Z0R7N/Linearity/pdf/full_M545D.jpg

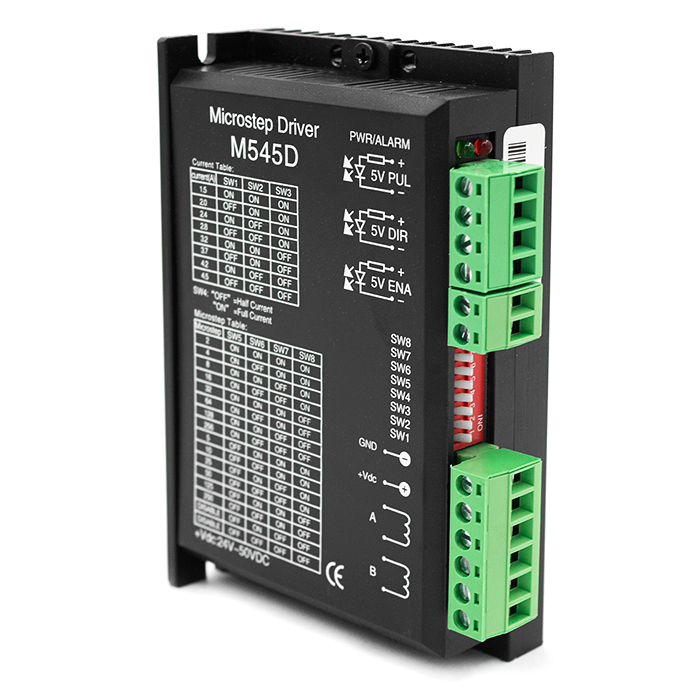
pdf/full_M545D.jpg
