Z0R7N/Linearity/3D/обработка/стойка/ncprograms/стойка д5.png

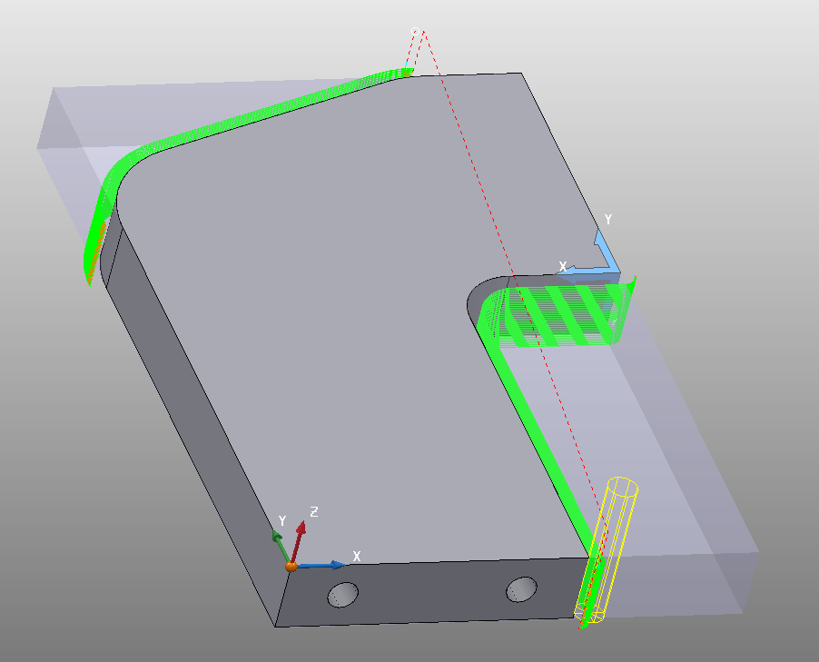
3D/обработка/стойка/ncprograms/стойка д5.png
