Z0R7N/Linearity/assets/angles.JPG

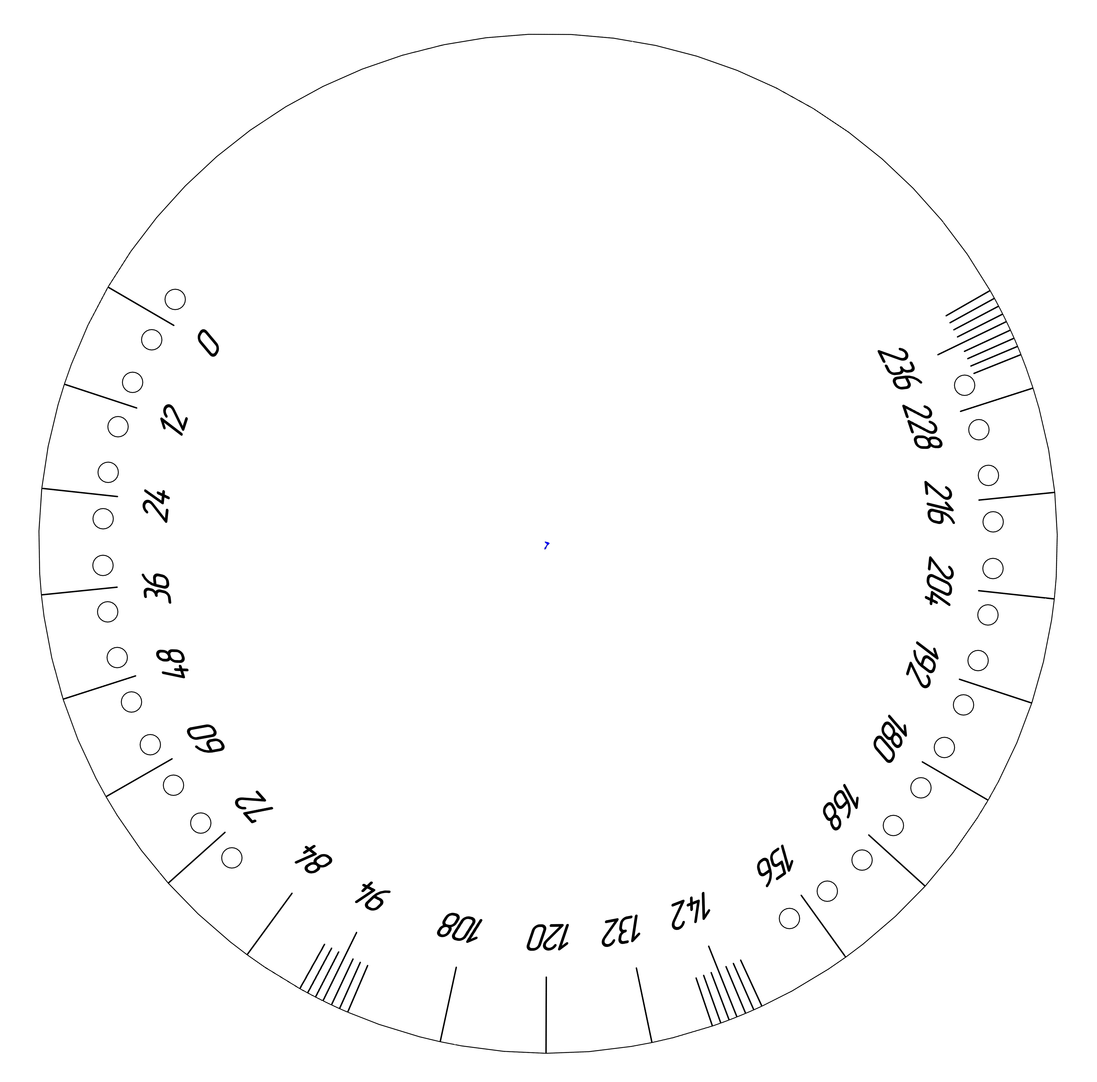
assets/angles.JPG
