Z0R7N/Linearity/assets/Nema 23.jpg

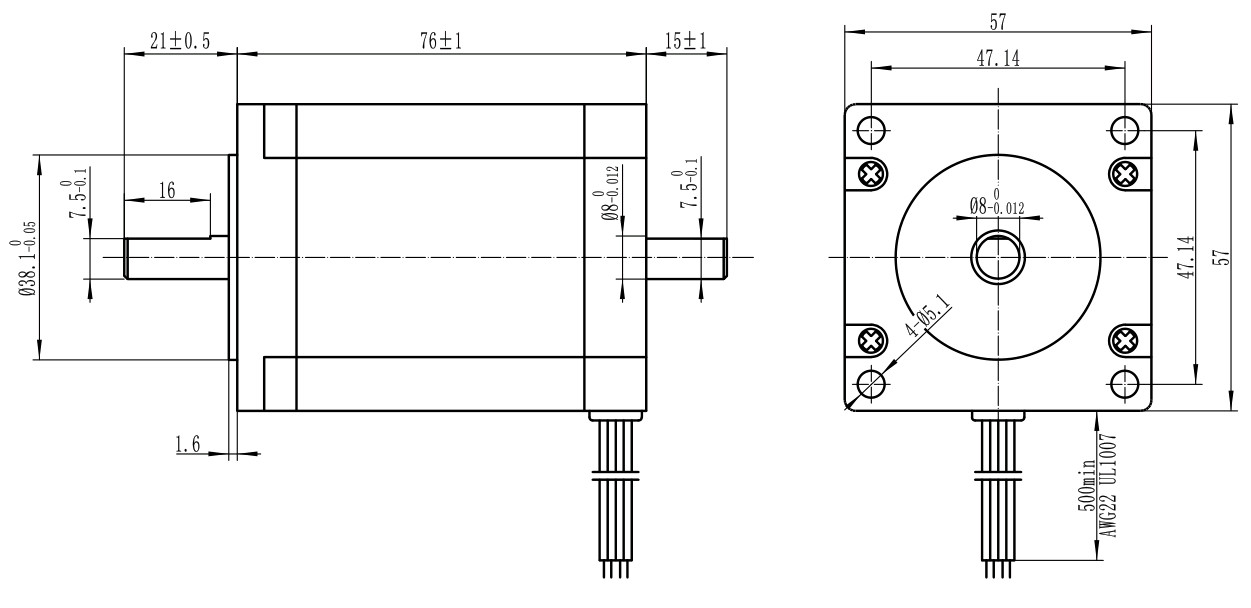
assets/Nema 23.jpg
