Z0R7N/Linearity/assets/plata pic/фреза 30гр.png

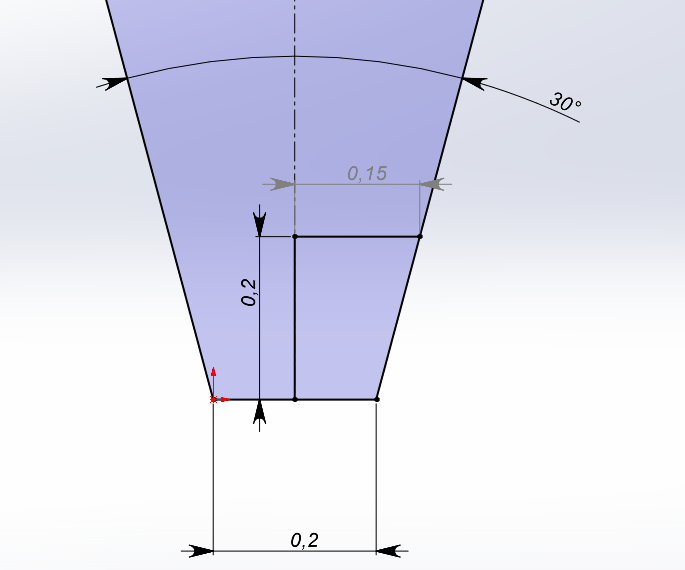
assets/plata pic/фреза 30гр.png
