Z0R7N/Linearity/assets/scheme for one angle.png

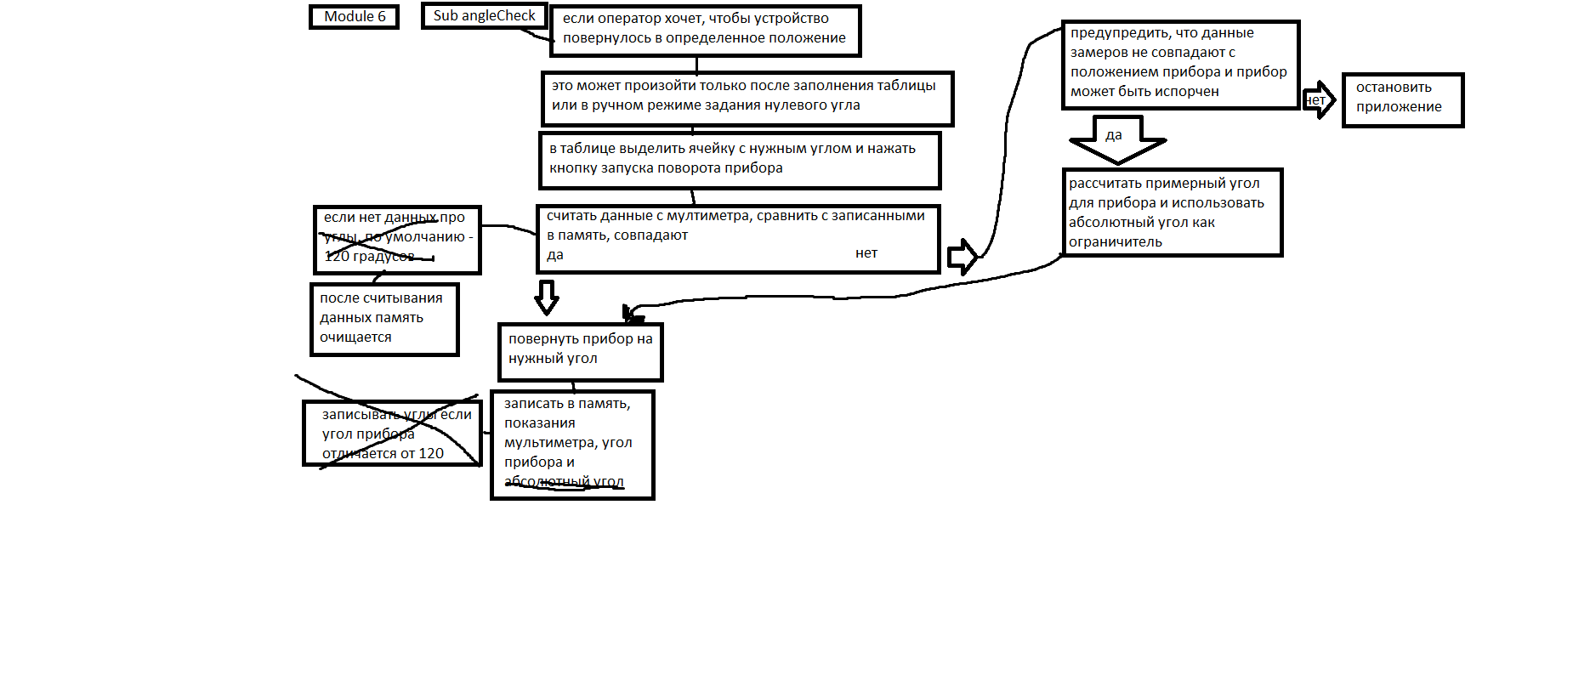
assets/scheme for one angle.png
