Z0R7N/Linearity/assets/table.png

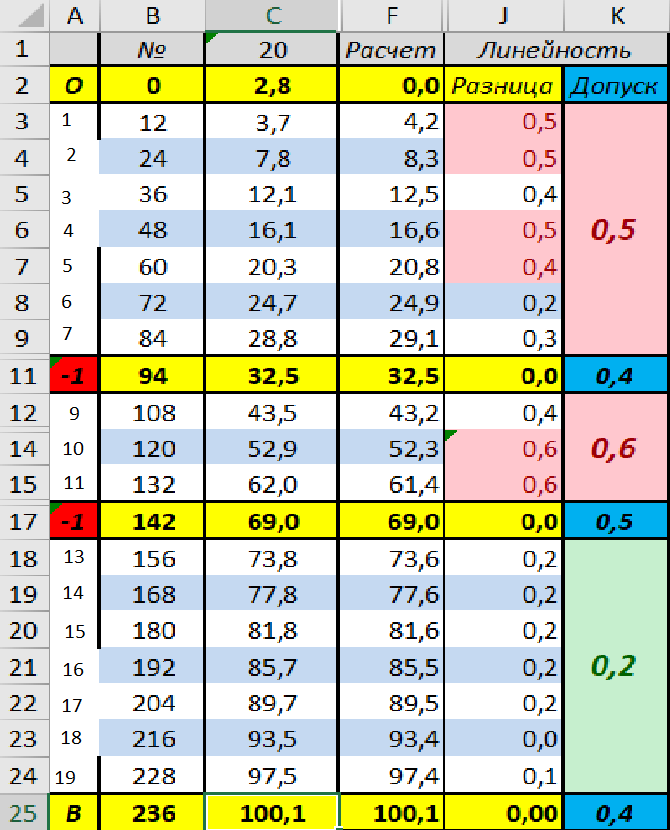
assets/table.png
