Z0R7N/Linearity/assets/usb B (2).gif

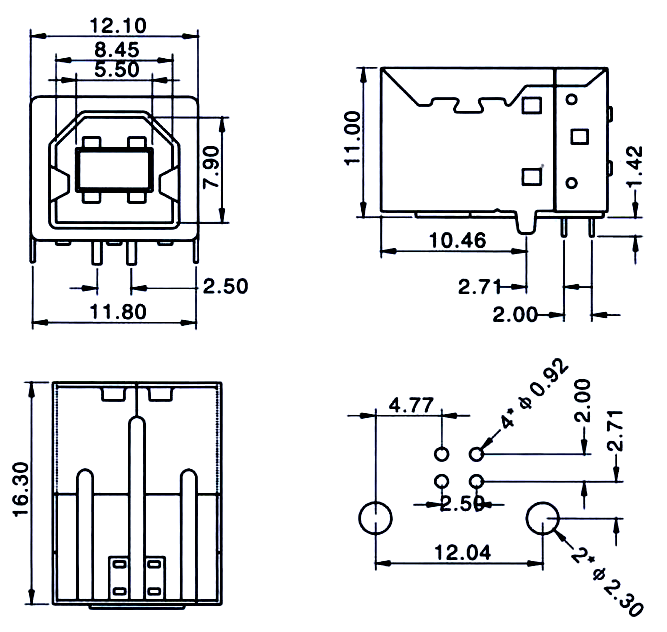
assets/usb B (2).gif
