Z0R7N/Linearity/assets/график.png

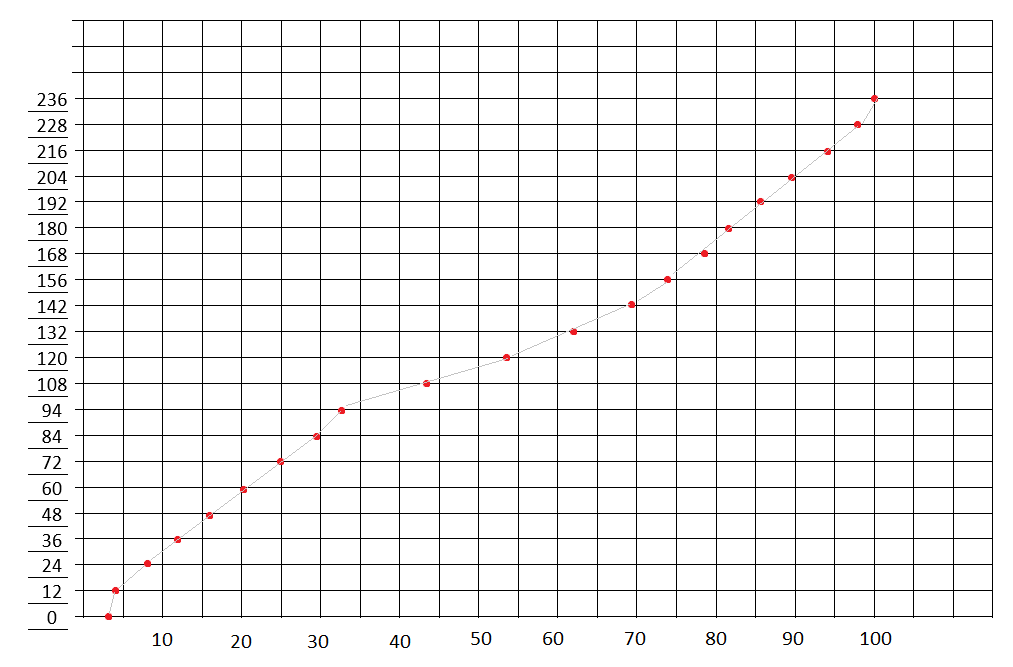
assets/график.png
