Z0R7N/Linearity/assets/прижим.jpg

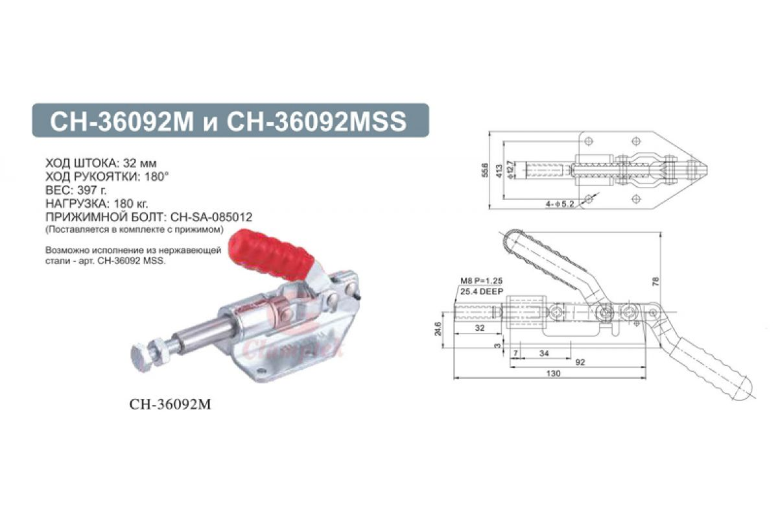
assets/прижим.jpg
