Z0R7N/Linearity/pdf/full_M545D_3.jpg

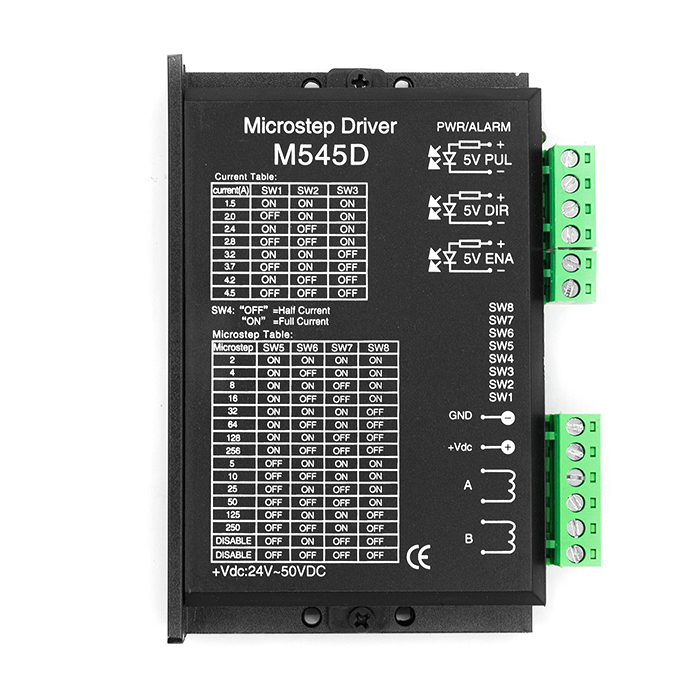
pdf/full_M545D_3.jpg
