Z0R7N/Linearity/3D/прижим.SLDPRT

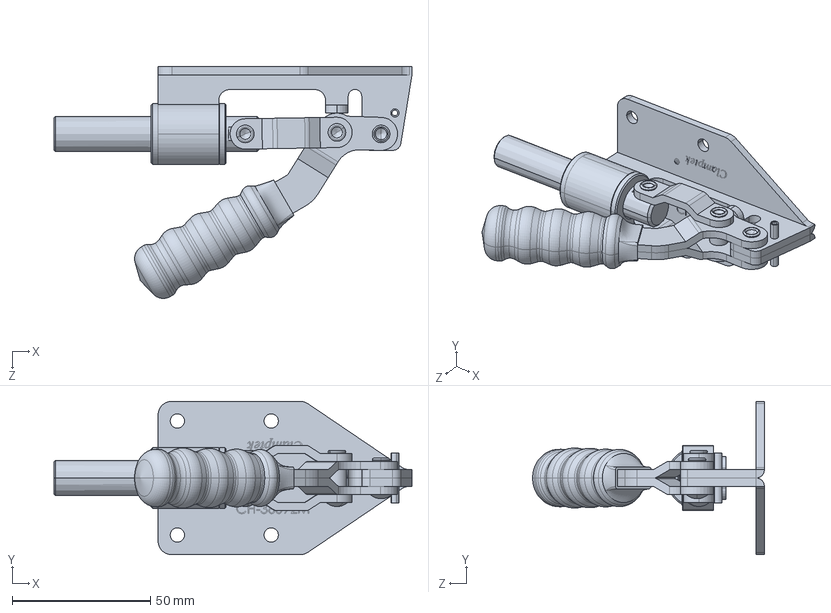
[picture p32: CAD file, 2022-04-15]
3D/прижим.SLDPRT
129.7 x 55.6 x 84.0 mm
