Z0R7N/Linearity/3D/п_крышка.stp.SLDPRT

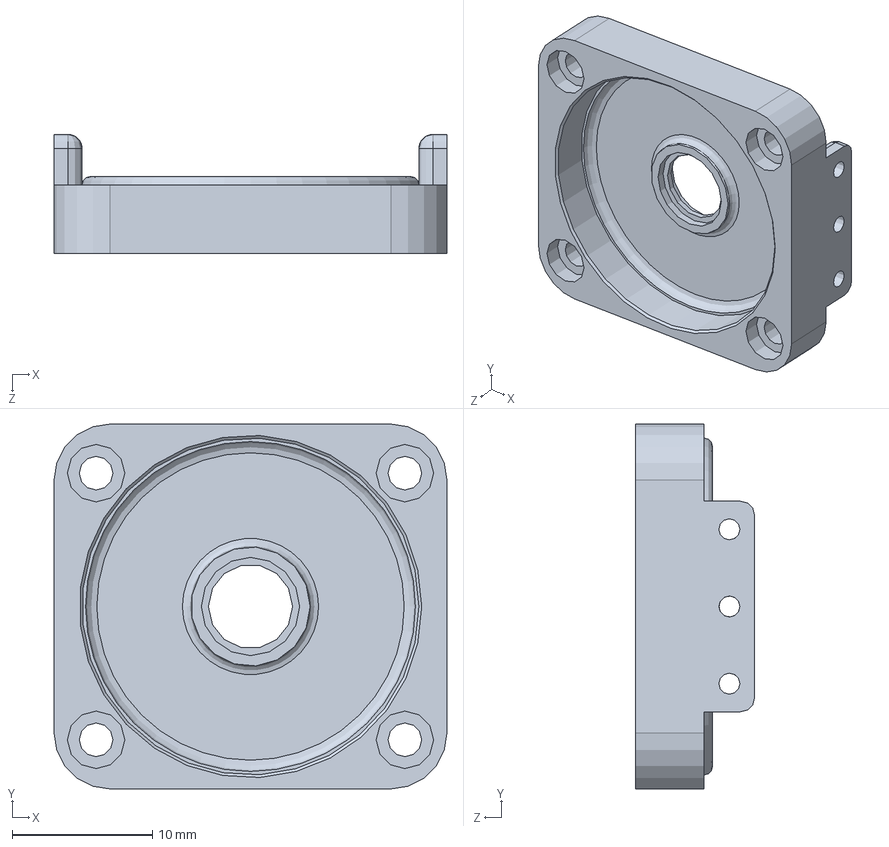
[picture p33: CAD file, 2022-04-15]
3D/п_крышка.stp.SLDPRT
28.0 x 26.0 x 8.50 mm
