Z0R7N/Linearity/3D/изолятор.SLDPRT

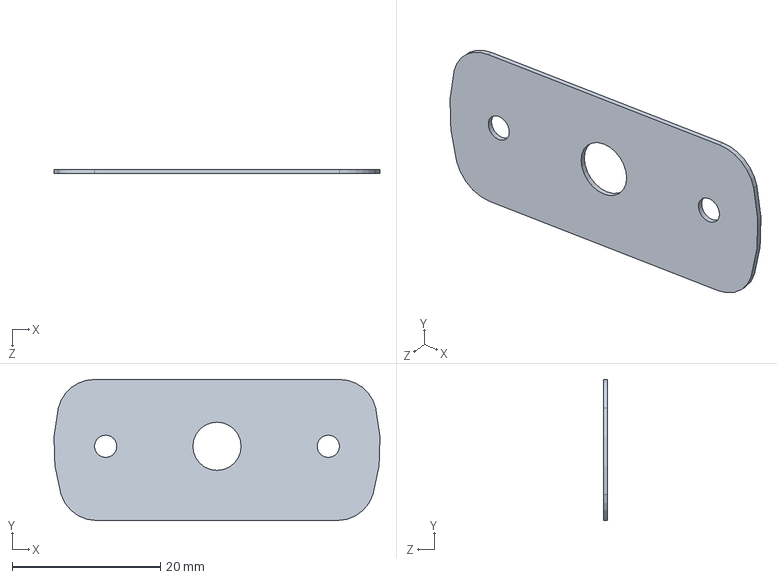
[picture p34: CAD file, 2022-04-15]
3D/изолятор.SLDPRT
43.9 x 19.0 x 0.6 mm
