Z0R7N/Linearity/3D/прижим крышки.SLDPRT

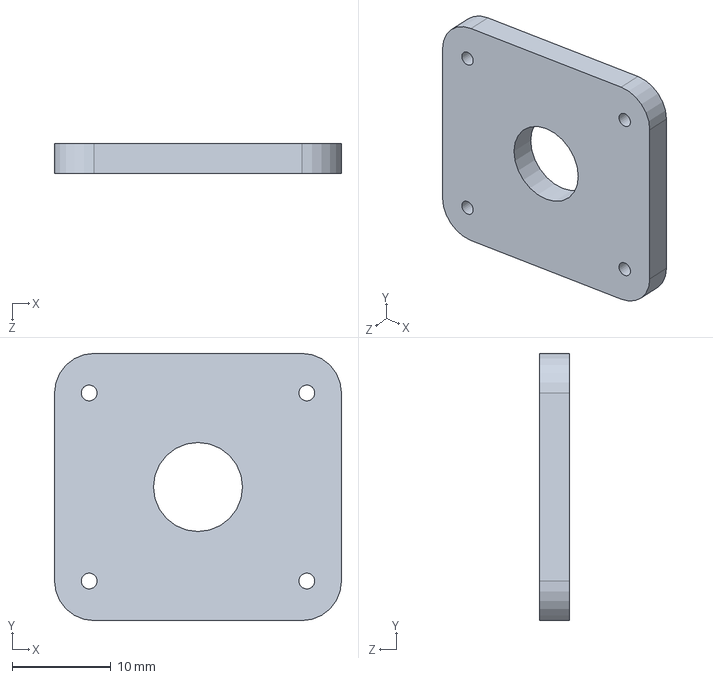
[picture p35: CAD file, 2022-04-12]
3D/прижим крышки.SLDPRT
29.0 x 27.0 x 3.00 mm
