Z0R7N/Linearity/3D/шайба прижима.SLDPRT

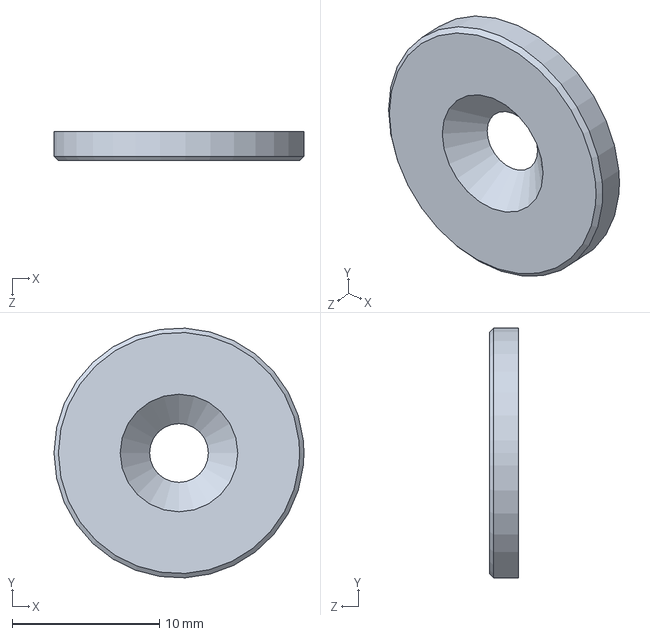
[picture p36: CAD file, 2022-04-12]
3D/шайба прижима.SLDPRT
17.0 x 17.0 x 2.00 mm
