Z0R7N/Linearity/3D/винт 2.SLDPRT

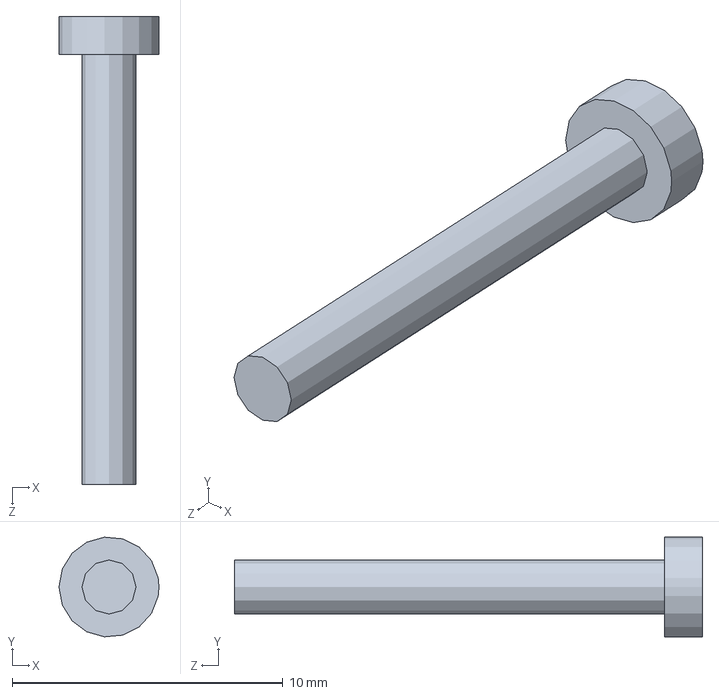
[picture p37: CAD file, 2022-04-12]
3D/винт 2.SLDPRT
3.70 x 3.68 x 17.3 mm
