Z0R7N/Linearity/3D/винт опора крышки.SLDPRT

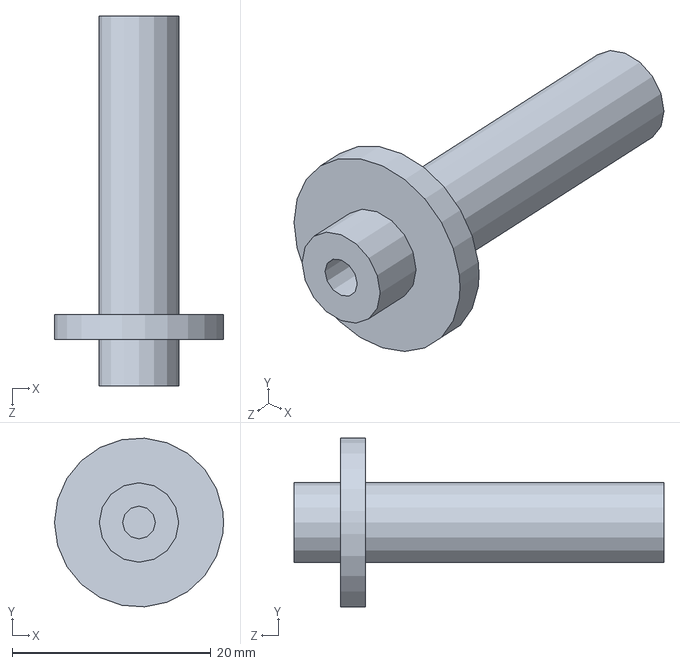
[picture p38: CAD file, 2022-04-12]
3D/винт опора крышки.SLDPRT
17.0 x 17.0 x 37.2 mm
