Z0R7N/Linearity/3D/стойка крышка.SLDPRT

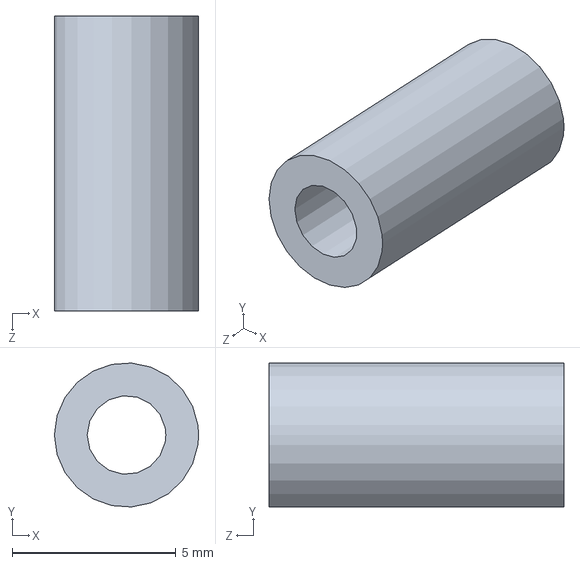
[picture p39: CAD file, 2022-04-12]
3D/стойка крышка.SLDPRT
4.40 x 4.39 x 9.00 mm
