Z0R7N/Linearity/3D/резина.SLDPRT

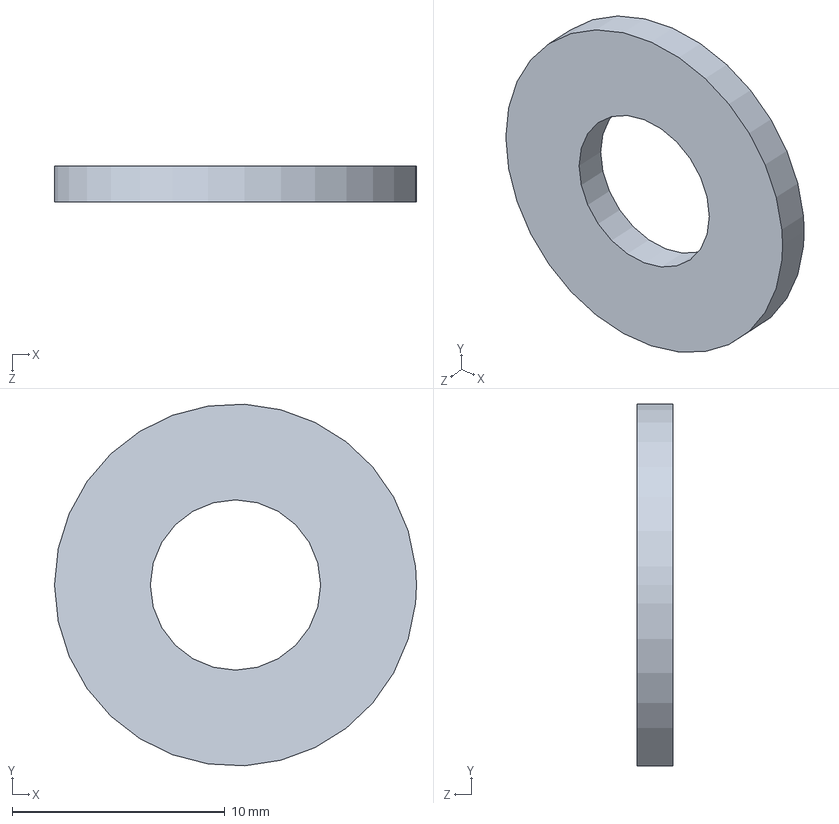
[picture p40: CAD file, 2022-04-12]
3D/резина.SLDPRT
17.0 x 17.0 x 1.70 mm
