Z0R7N/Linearity/3D/плата для замеров дорожки.SLDPRT

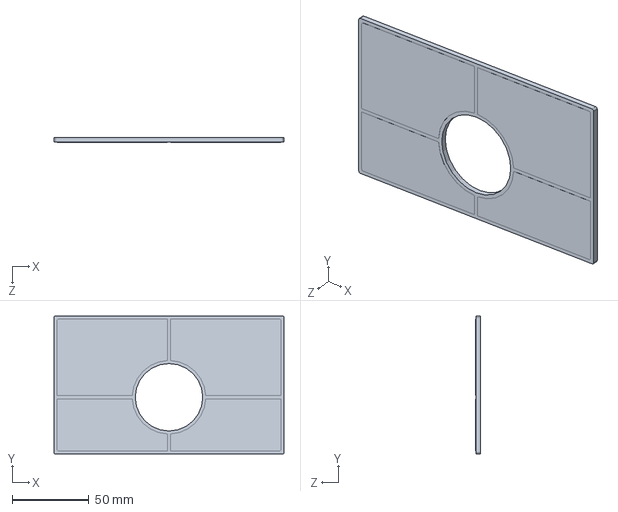
[picture p41: CAD file, 2022-04-07]
3D/плата для замеров дорожки.SLDPRT
150.0 x 90.0 x 3.00 mm
