Z0R7N/Linearity/3D/фиксатор.SLDPRT

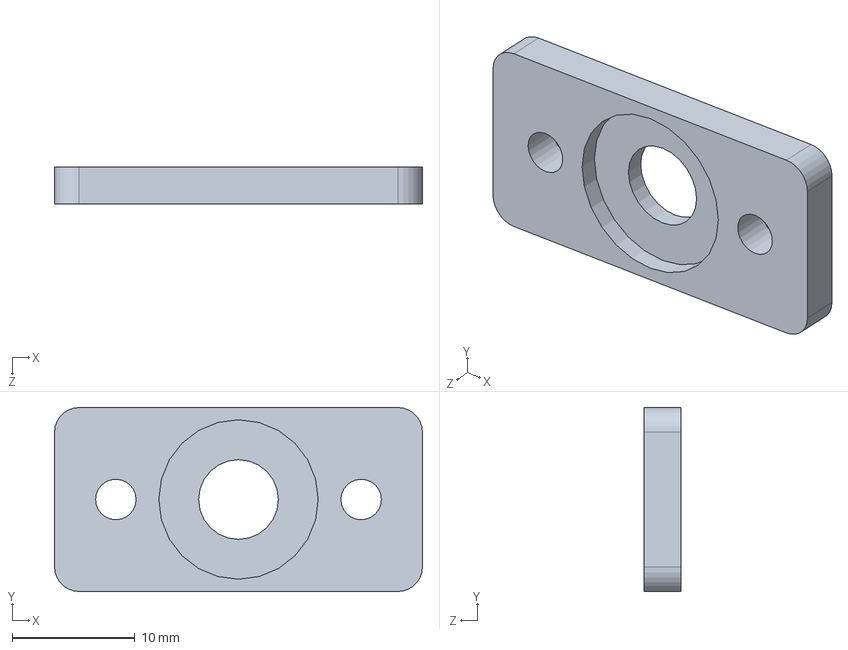
[picture p42: CAD file, 2022-03-29]
3D/фиксатор.SLDPRT
30.0 x 15.0 x 3.00 mm
