Z0R7N/Linearity/3D/гайка.SLDPRT

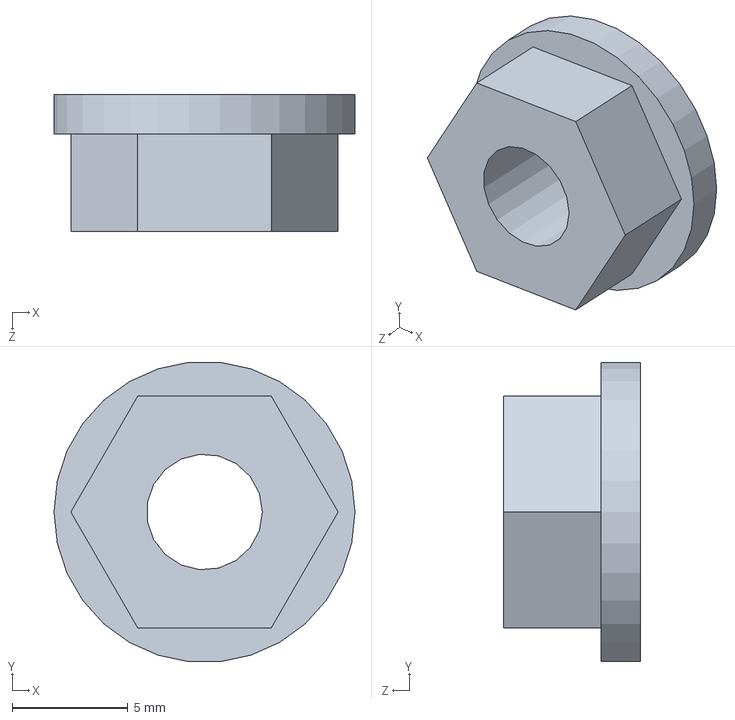
[picture p43: CAD file, 2022-03-16]
3D/гайка.SLDPRT
13.0 x 12.9 x 5.90 mm
