Z0R7N/Linearity/3D/держатель резистора.SLDPRT

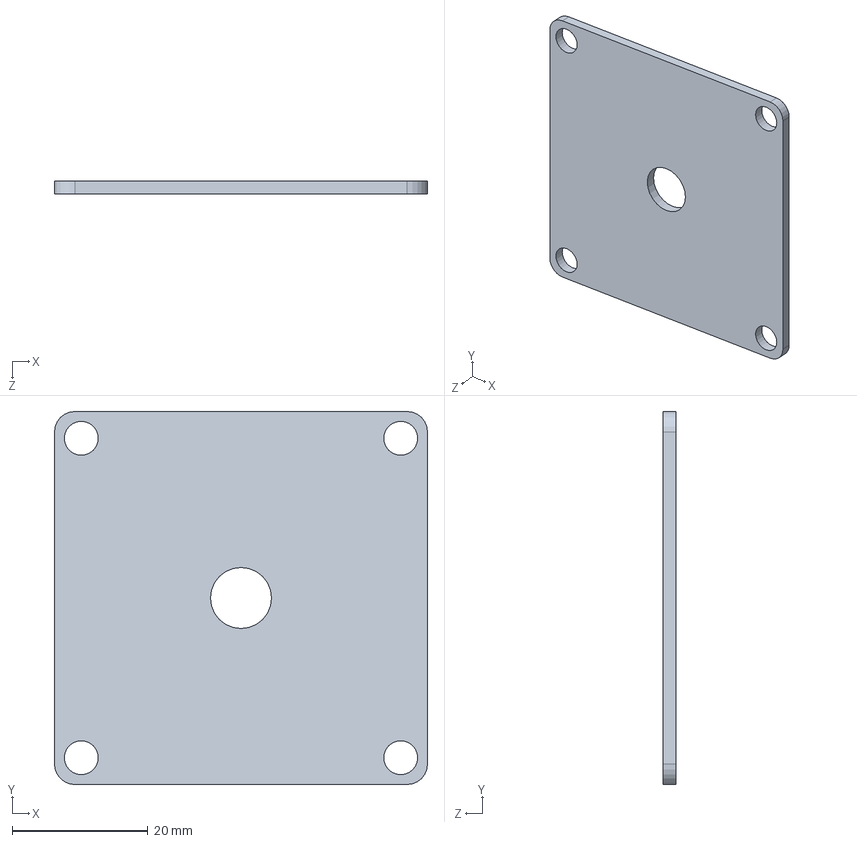
[picture p44: CAD file, 2022-02-24]
3D/держатель резистора.SLDPRT
55.0 x 55.0 x 1.90 mm
