Z0R7N/Linearity/3D/резистор.SLDPRT

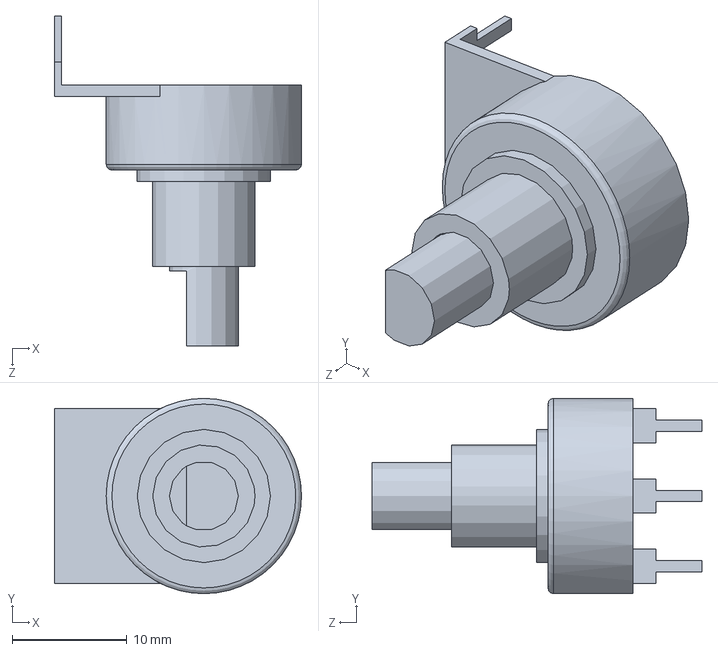
[picture p45: CAD file, 2022-02-24]
3D/резистор.SLDPRT
21.5 x 17.0 x 28.7 mm
