Z0R7N/Linearity/3D/стойка резистора.SLDPRT

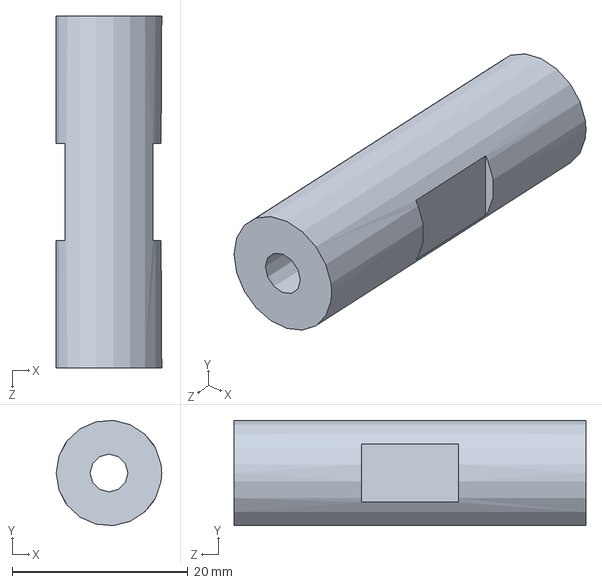
[picture p46: CAD file, 2022-02-24]
3D/стойка резистора.SLDPRT
12.0 x 12.0 x 40.0 mm
