Z0R7N/Linearity/3D/стол.SLDPRT

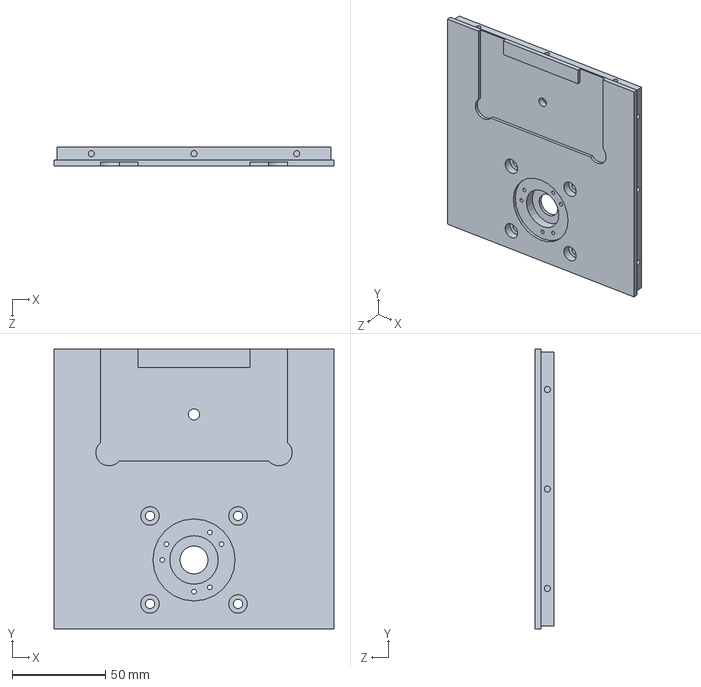
[picture p47: CAD file, 2022-02-03]
3D/стол.SLDPRT
150.0 x 150.0 x 10.0 mm
