Z0R7N/Linearity/3D/держатель энкодера стойка.SLDPRT

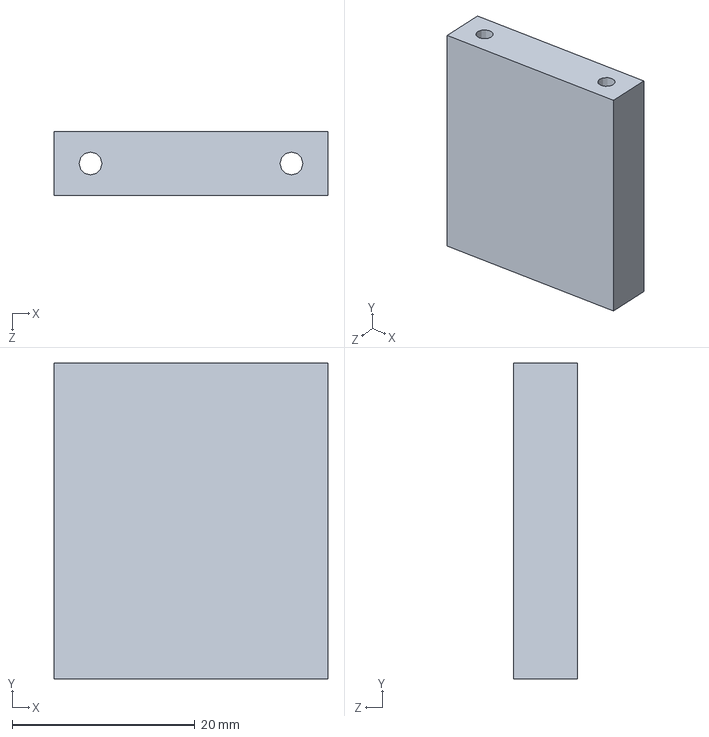
[picture p48: CAD file, 2021-12-29]
3D/держатель энкодера стойка.SLDPRT
30.0 x 34.6 x 7.00 mm
