Z0R7N/Linearity/3D/держатель энкодера крышка.SLDPRT

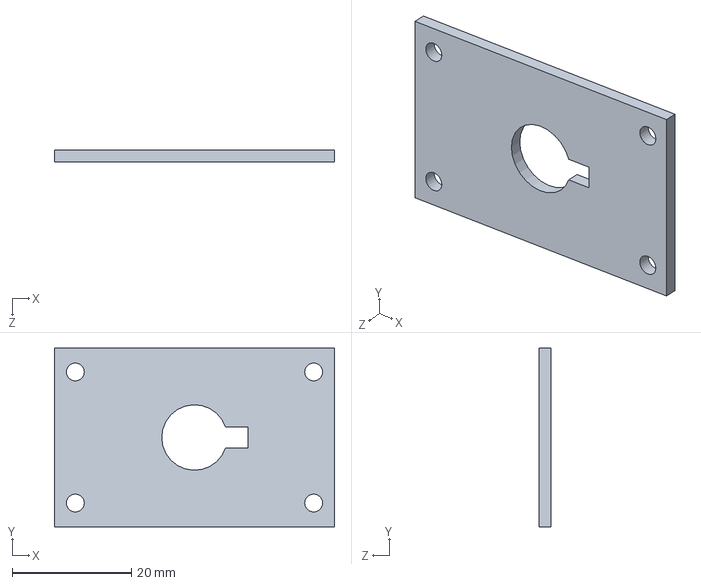
[picture p49: CAD file, 2021-12-29]
3D/держатель энкодера крышка.SLDPRT
47.0 x 30.0 x 2.00 mm
