Z0R7N/Linearity/3D/Nema 23.SLDPRT

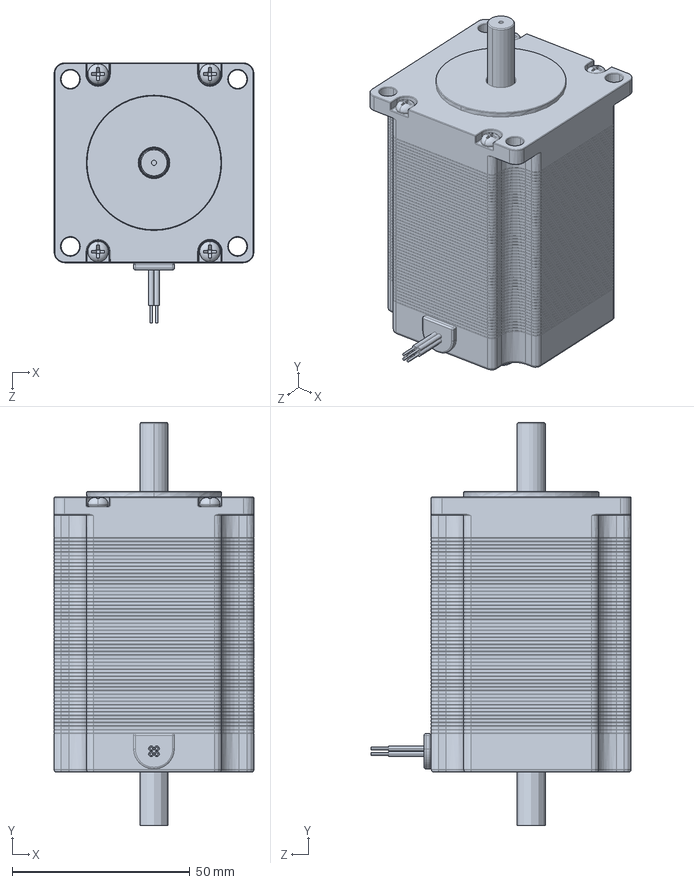
[picture p50: CAD file, 2021-12-29]
3D/Nema 23.SLDPRT
56.3 x 113.5 x 73.3 mm
