Z0R7N/Linearity/3D/держатель энкодера пластина.SLDPRT

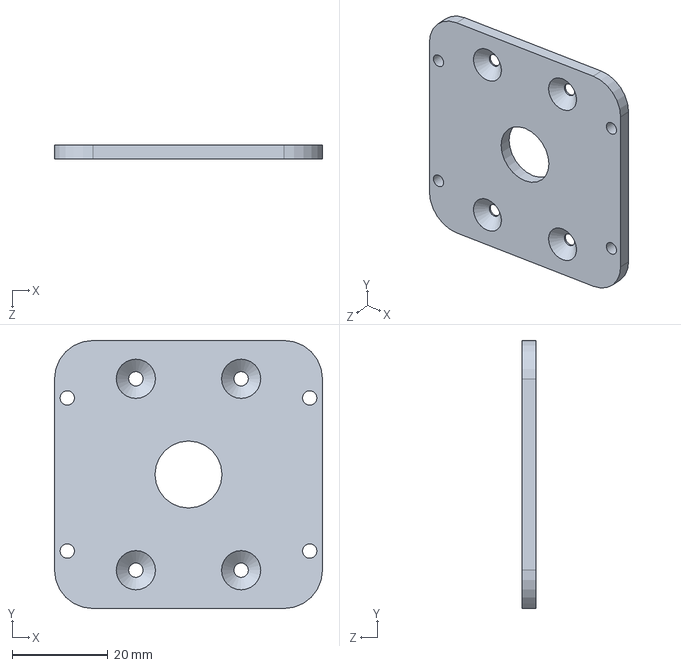
[picture p51: CAD file, 2021-12-29]
3D/держатель энкодера пластина.SLDPRT
56.0 x 56.0 x 3.00 mm
