Z0R7N/Linearity/3D/стойка прижима держатель.SLDPRT

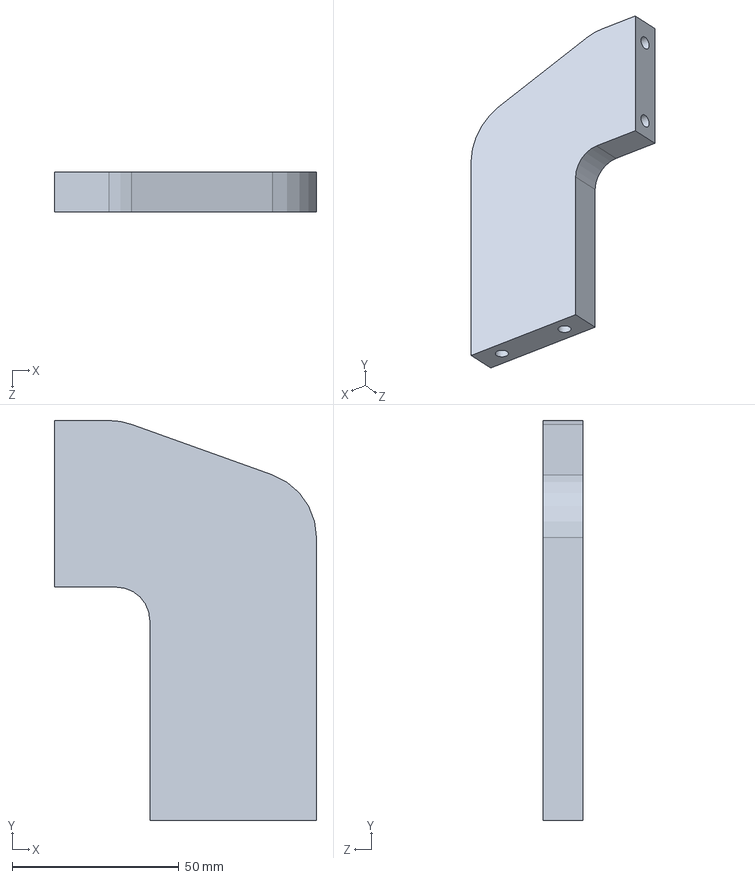
[picture p52: CAD file, 2021-12-15]
3D/стойка прижима держатель.SLDPRT
78.6 x 120.0 x 12.0 mm
