Z0R7N/Linearity/3D/драйвер.SLDPRT

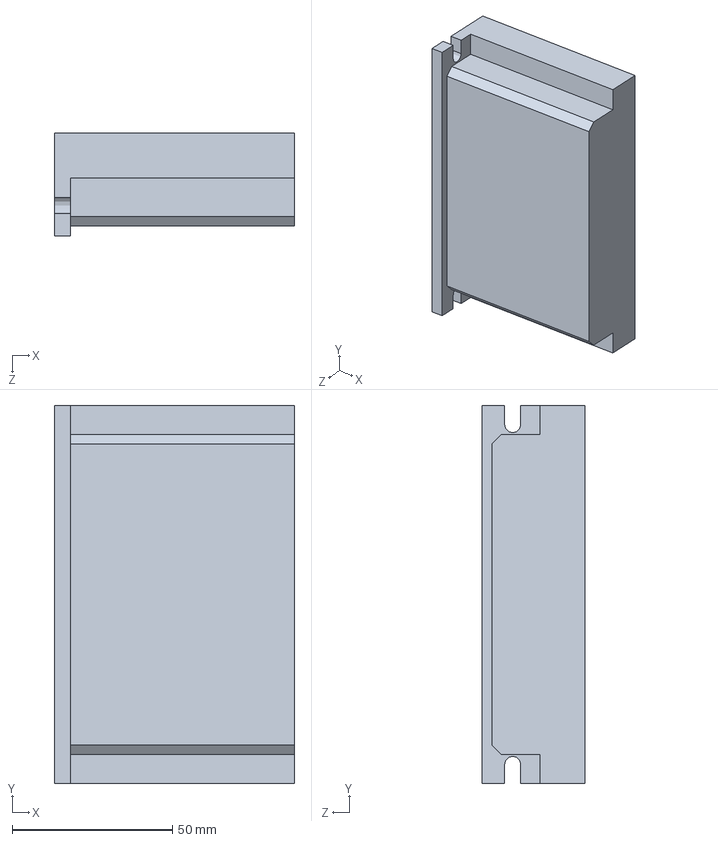
[picture p53: CAD file, 2021-12-15]
3D/драйвер.SLDPRT
75.0 x 118.0 x 32.0 mm
