Z0R7N/Linearity/3D/муфта.SLDPRT

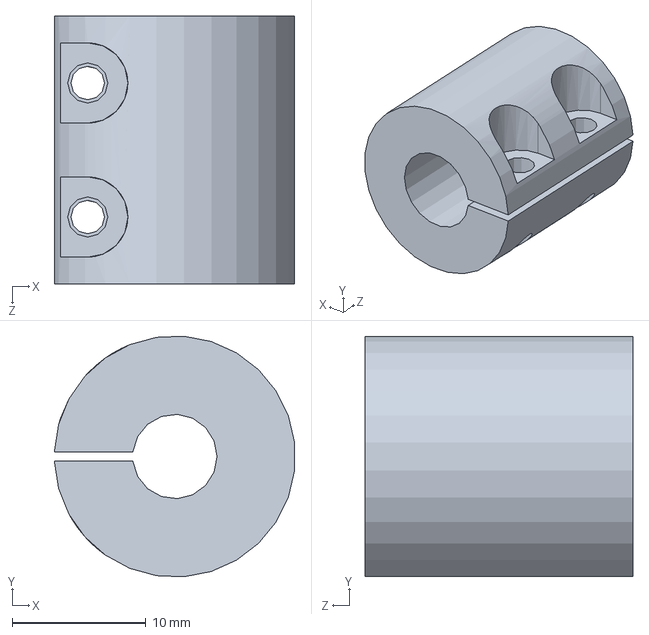
[picture p54: CAD file, 2021-12-15]
3D/муфта.SLDPRT
17.9 x 17.9 x 20.0 mm
