Z0R7N/Linearity/3D/ось корпус.SLDPRT

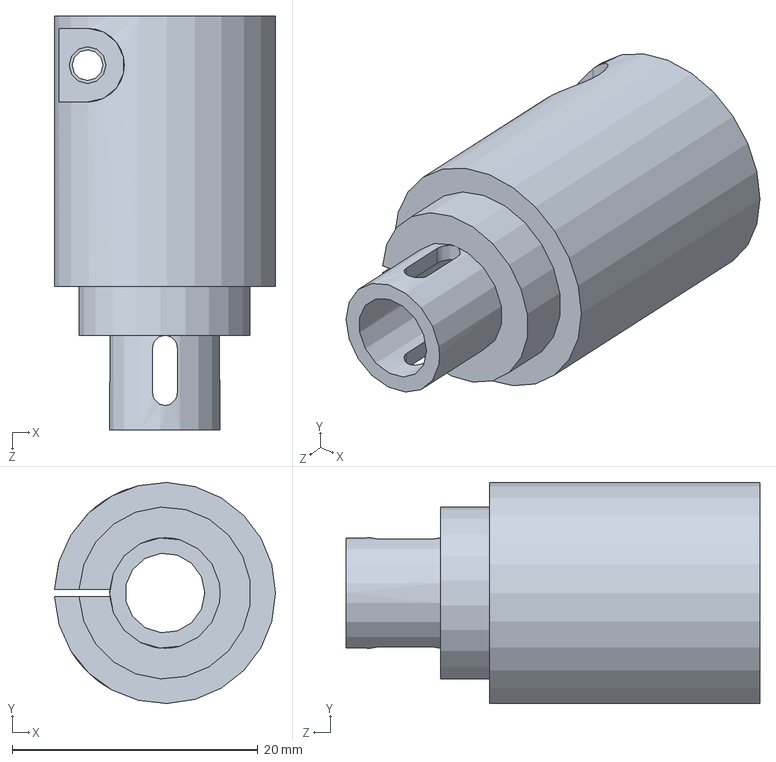
[picture p55: CAD file, 2021-12-15]
3D/ось корпус.SLDPRT
18.0 x 18.0 x 33.7 mm
