Z0R7N/Linearity/3D/плата.SLDPRT

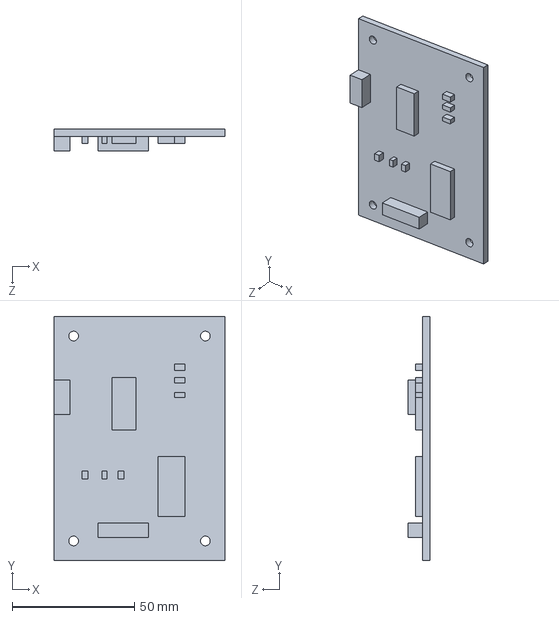
[picture p56: CAD file, 2021-12-15]
3D/плата.SLDPRT
70.0 x 100.0 x 9.00 mm
