Z0R7N/Linearity/3D/п_корпус.stp.SLDPRT

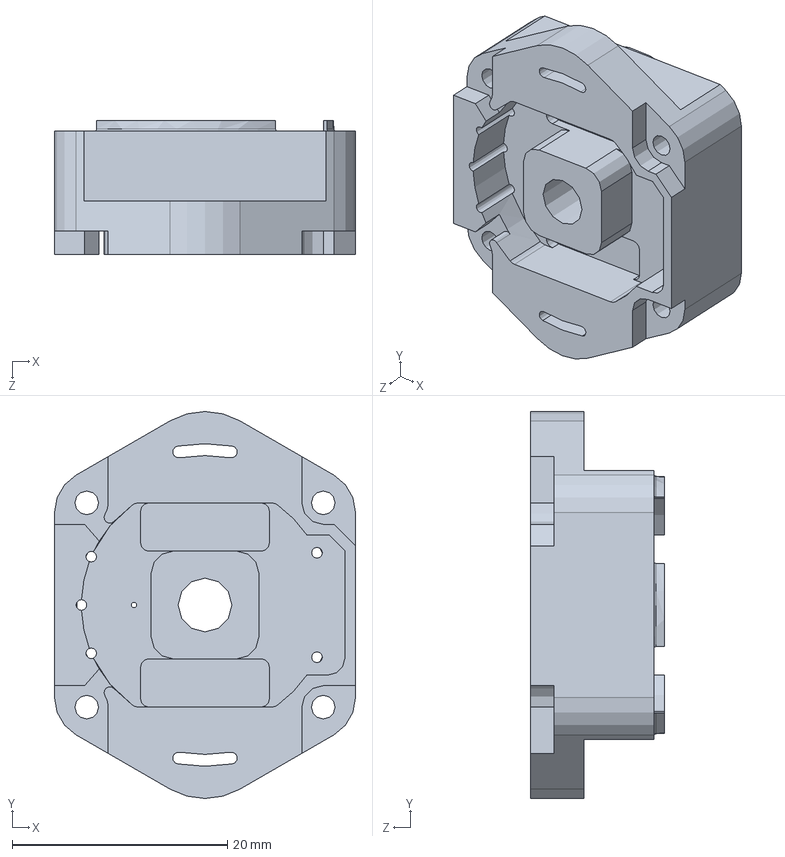
[picture p57: CAD file, 2021-12-15]
3D/п_корпус.stp.SLDPRT
28.0 x 36.0 x 12.5 mm
