Z0R7N/Linearity/3D/стойка для платы.SLDPRT

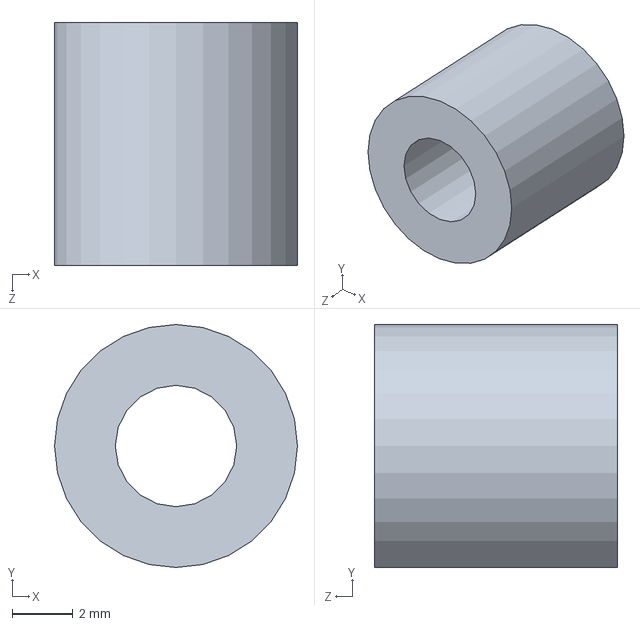
[picture p58: CAD file, 2021-12-15]
3D/стойка для платы.SLDPRT
8.00 x 8.00 x 8.00 mm
