Z0R7N/Linearity/3D/стойка прижима основа.SLDPRT

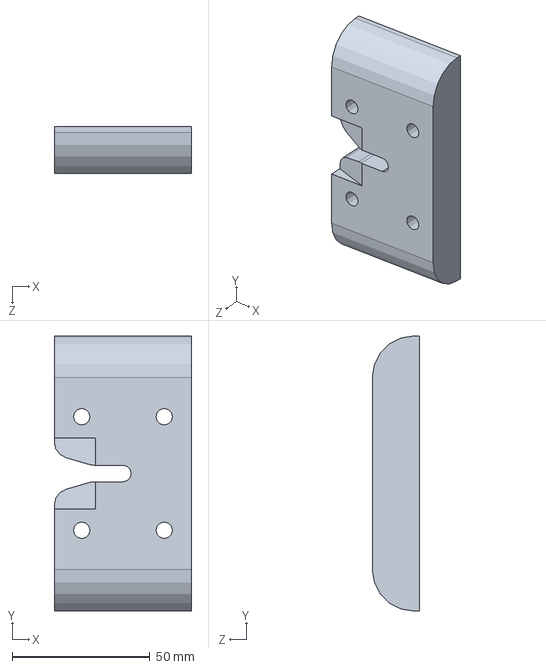
[picture p59: CAD file, 2021-12-15]
3D/стойка прижима основа.SLDPRT
50.0 x 100.0 x 17.2 mm
