Z0R7N/Linearity/3D/стопор оси.SLDPRT

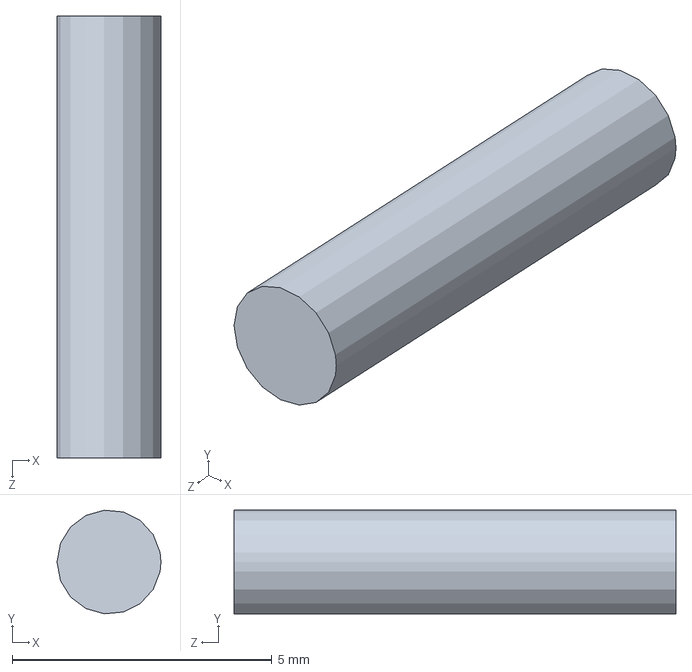
[picture p60: CAD file, 2021-12-15]
3D/стопор оси.SLDPRT
2.00 x 1.99 x 8.50 mm
