Z0R7N/Linearity/3D/винт.SLDPRT

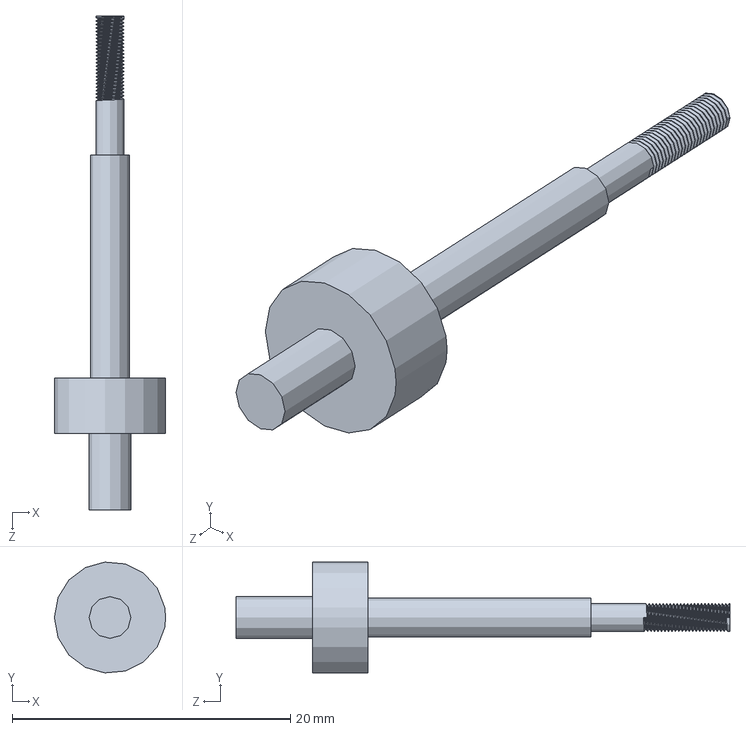
[picture p61: CAD file, 2021-12-15]
3D/винт.SLDPRT
8.00 x 7.97 x 35.5 mm
