Z0R7N/Linearity/3D/подшипник.SLDPRT

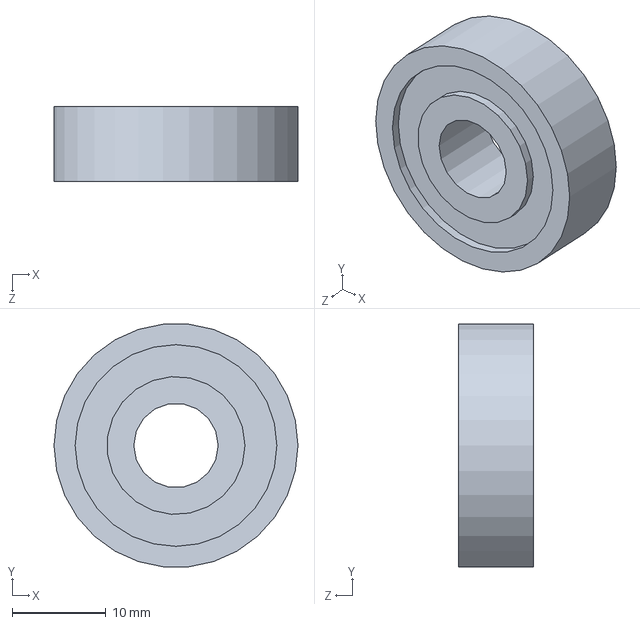
[picture p62: CAD file, 2021-12-15]
3D/подшипник.SLDPRT
26.0 x 25.9 x 8.00 mm
