Z0R7N/Linearity/3D/ось.SLDPRT

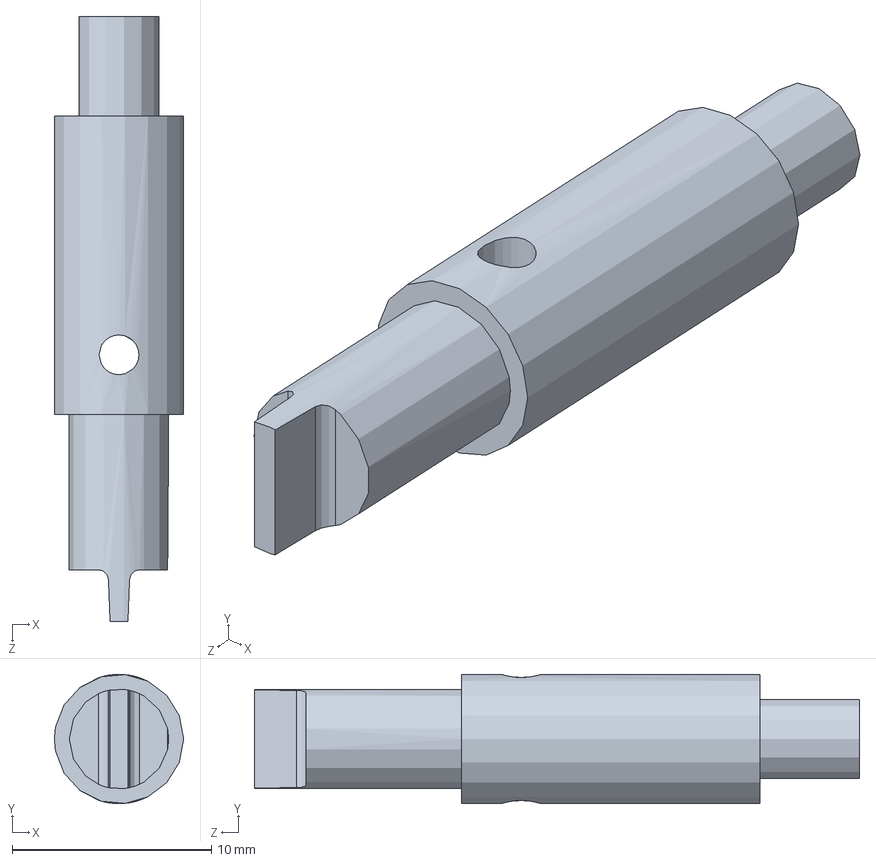
[picture p63: CAD file, 2021-12-15]
3D/ось.SLDPRT
6.50 x 6.50 x 30.4 mm
