Z0R7N/Linearity/3D/основание.SLDPRT

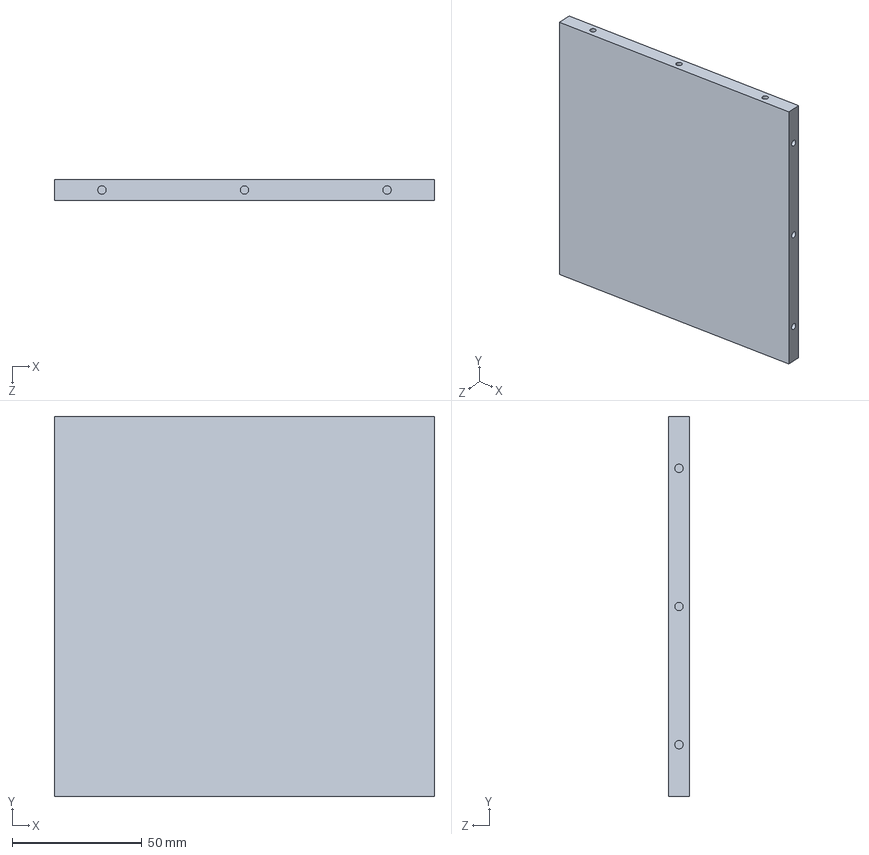
[picture p64: CAD file, 2021-12-15]
3D/основание.SLDPRT
146.6 x 146.6 x 8.00 mm
