Z0R7N/Linearity/3D/энкодер.SLDPRT

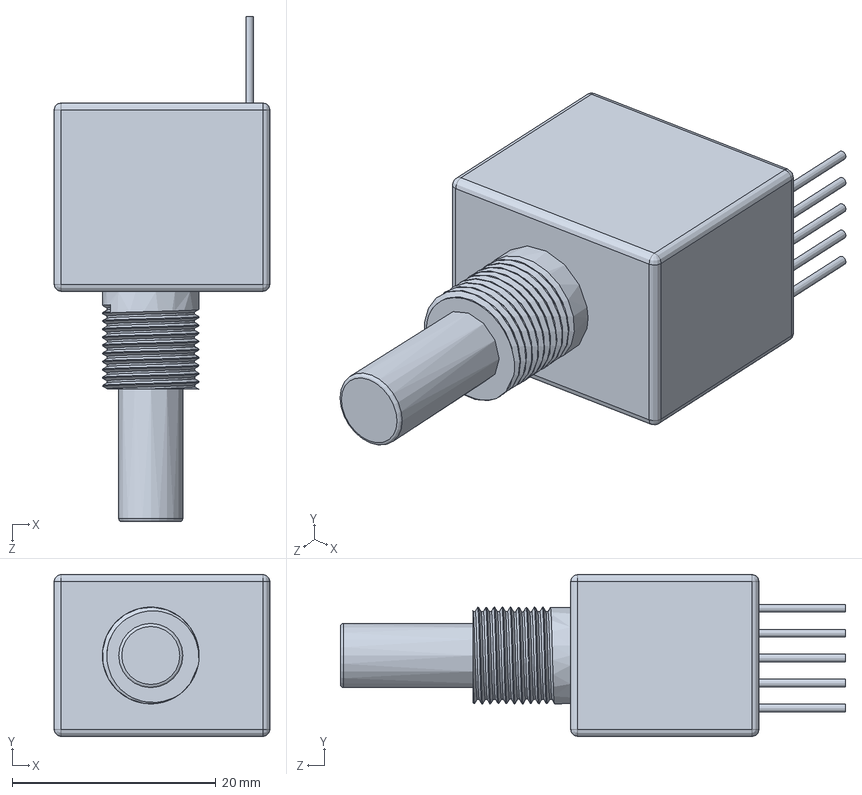
[picture p65: CAD file, 2021-12-15]
3D/энкодер.SLDPRT
21.2 x 15.9 x 49.6 mm
