Z0R7N/Linearity/assets/scheme for manual.png

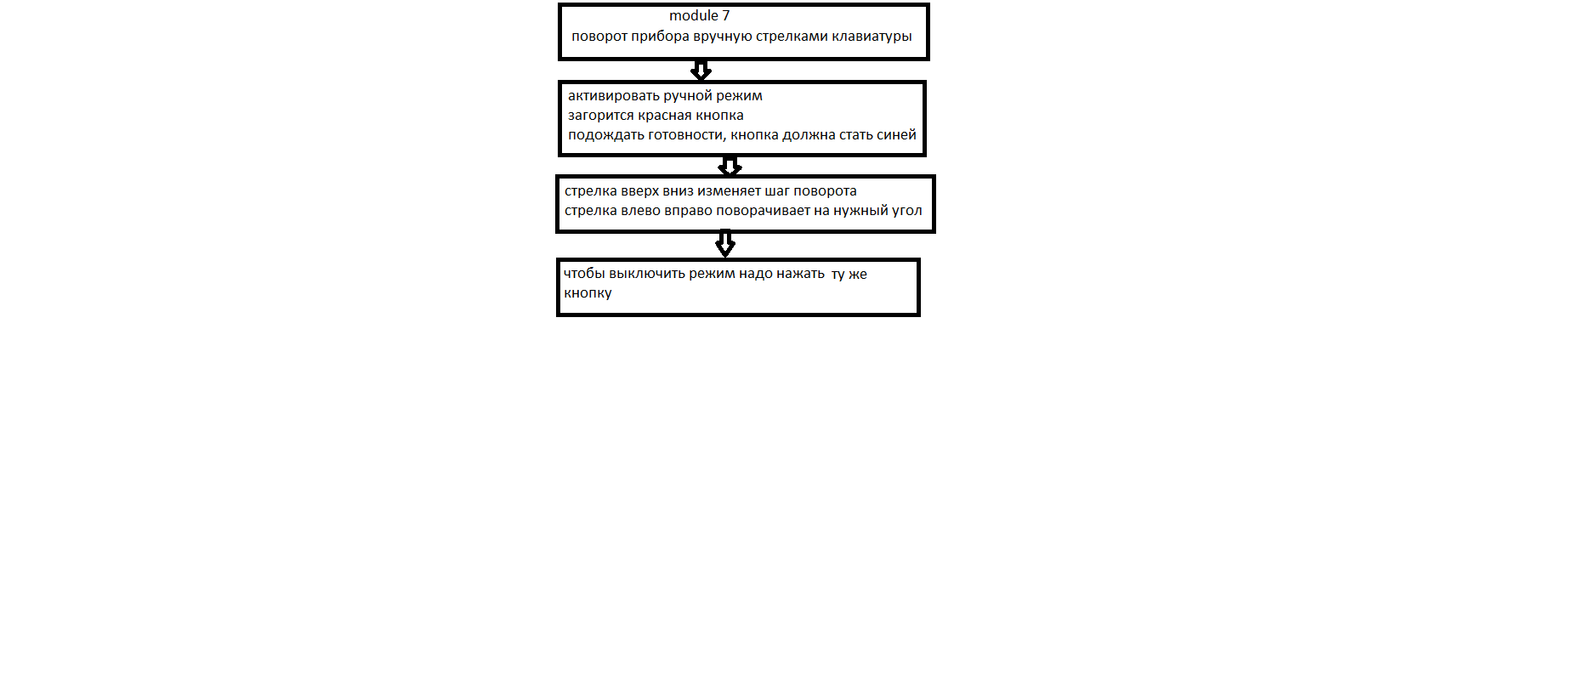
assets/scheme for manual.png
